kvtorp/openscad-case/dimensions.scad

$fn = 256;

/* Tiny case */
/*
textOnLid = "C";
textSize = 20;
length = 50;
width = 50;
height = 40;
thickness = 2;
withInset = false;
cornerRadius = 10;
*/

/* DJI Osmo Action 4 case */
textOnLid = "CAMERA";
textSize = 20;
length = 140;
width = 140;
height = 45;
thickness = 2;
withInset = true;
cornerRadius = 10;
// Plus the cutout in file Parts/box-inset.scad
