kvtorp/openscad-case/lid-inset-patches.scad

include <dimensions.scad>

use <case.scad>

InsertPatches(length, width, cornerRadius, thickness);
