kvtorp/openscad-case/lid-inset.scad

include <dimensions.scad>

use <case.scad>

LidInsert(length, width, cornerRadius, thickness);
