kvtorp/openscad-case/lid-text.scad

include <dimensions.scad>

use <case.scad>

color("blue")
LidText(length, width, textOnLid, textSize);
