kvtorp/openscad-case/lid.scad

include <dimensions.scad>

use <case.scad>

Lid(length, width, cornerRadius, thickness, textOnLid, textSize, withInset);
