kvtorp/openscad-case/Parts/box-supports.scad

include <../dimensions.scad>

use <../Case/case.scad>

AnslagSupport(length, height, cornerRadius);
