kvtorp/openscad-case/Parts/box.scad

include <../dimensions.scad>

use <../Case/case.scad>

Box(length, width, height, cornerRadius, thickness, withInset);
