kvtorp/openscad-case/Parts/lid-buckles.scad

include <../dimensions.scad>

use <../Case/case.scad>

Buckles(length, cornerRadius);
