kvtorp/openscad-case/Parts/lid-inset-patches.scad

include <../dimensions.scad>

use <../Case/case.scad>

InsertPatches(length, width, cornerRadius, thickness);
