kvtorp/openscad-case/Parts/lid-inset.scad

include <../dimensions.scad>

use <../Case/case.scad>

LidInsert(length, width, cornerRadius, thickness);
