kvtorp/openscad-case/Parts/lid-text.scad

include <../dimensions.scad>

use <../Case/case.scad>

color("blue")
LidText(length, width, textOnLid, textSize);
