kvtorp/openscad-case/Parts/lid.scad

include <../dimensions.scad>

use <../Case/case.scad>

Lid(length, width, cornerRadius, thickness, textOnLid, textSize, withInset);
